madebybye/esp32-mac/renders/fit_gauge.png

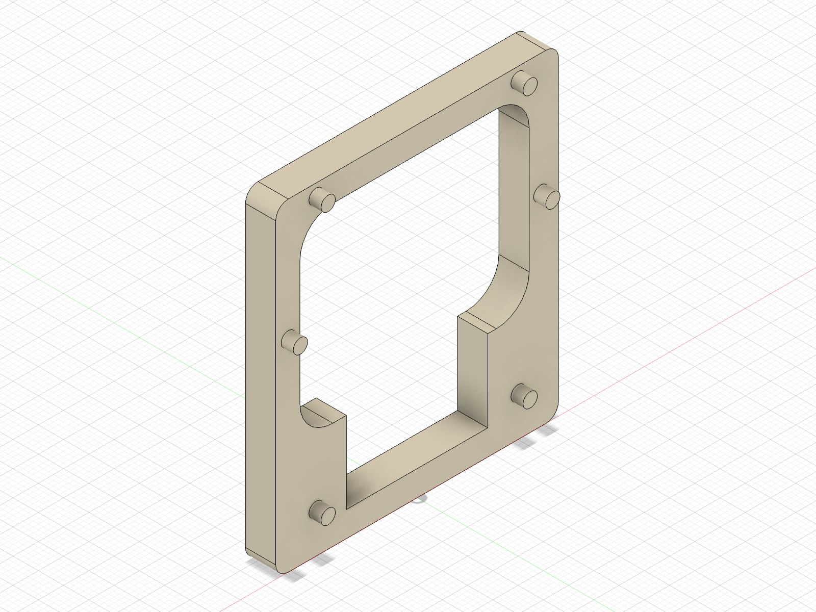
renders/fit_gauge.png
