madebybye/esp32-mac/renders/section.png

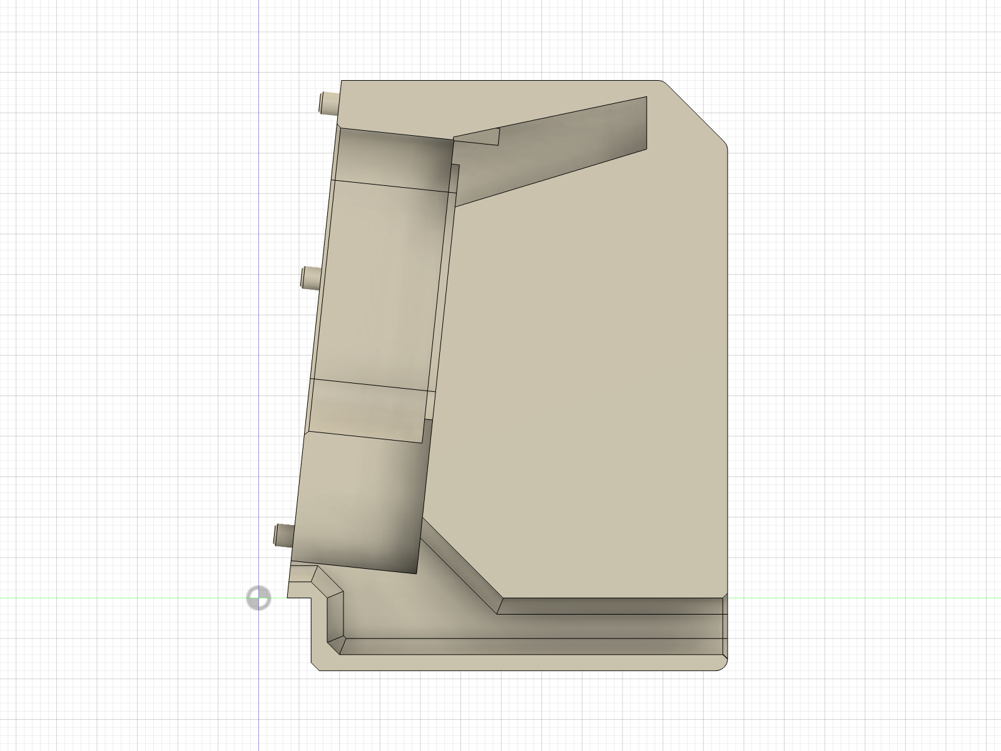
renders/section.png
