madebybye/esp32-mac/renders/parts/Body_front.png

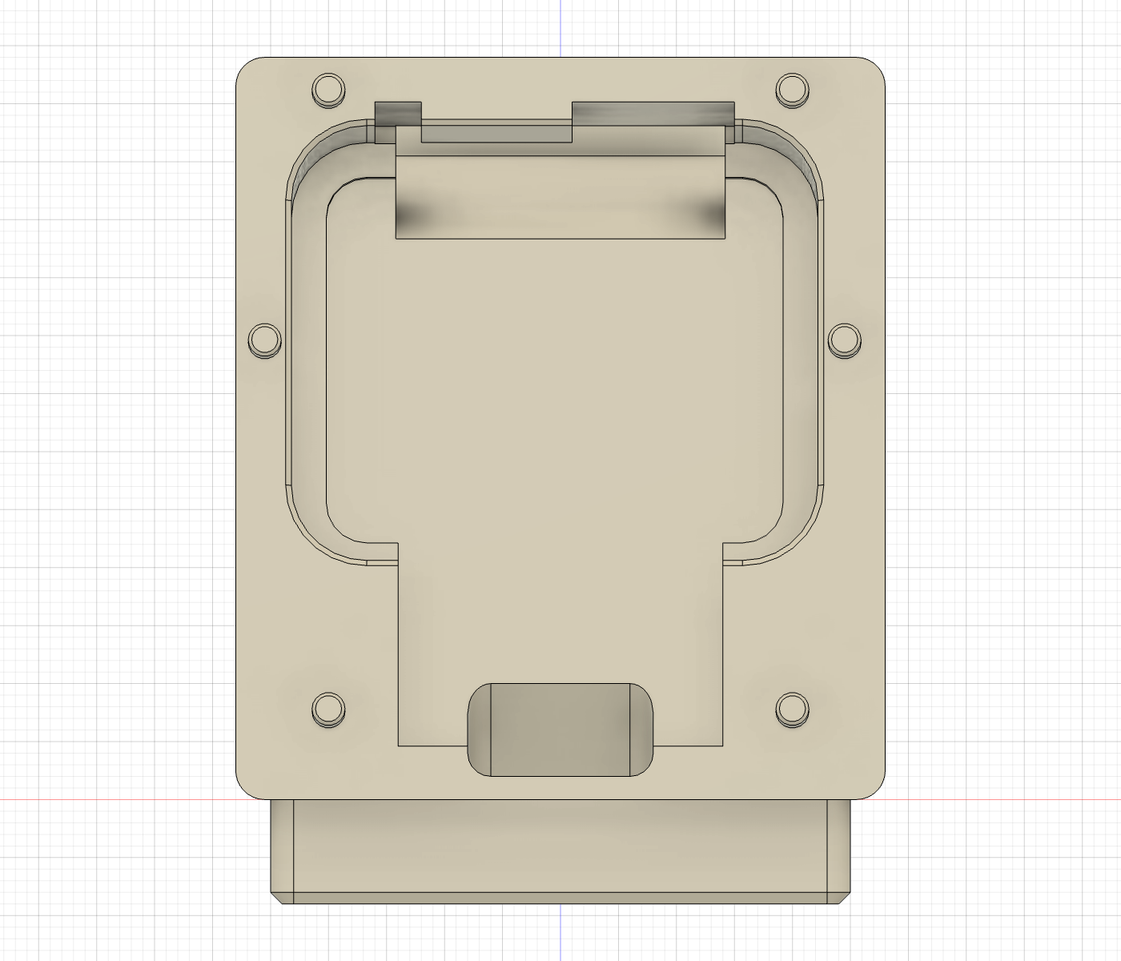
renders/parts/Body_front.png
