madebybye/esp32-mac/renders/parts/Body_iso-top-right.png

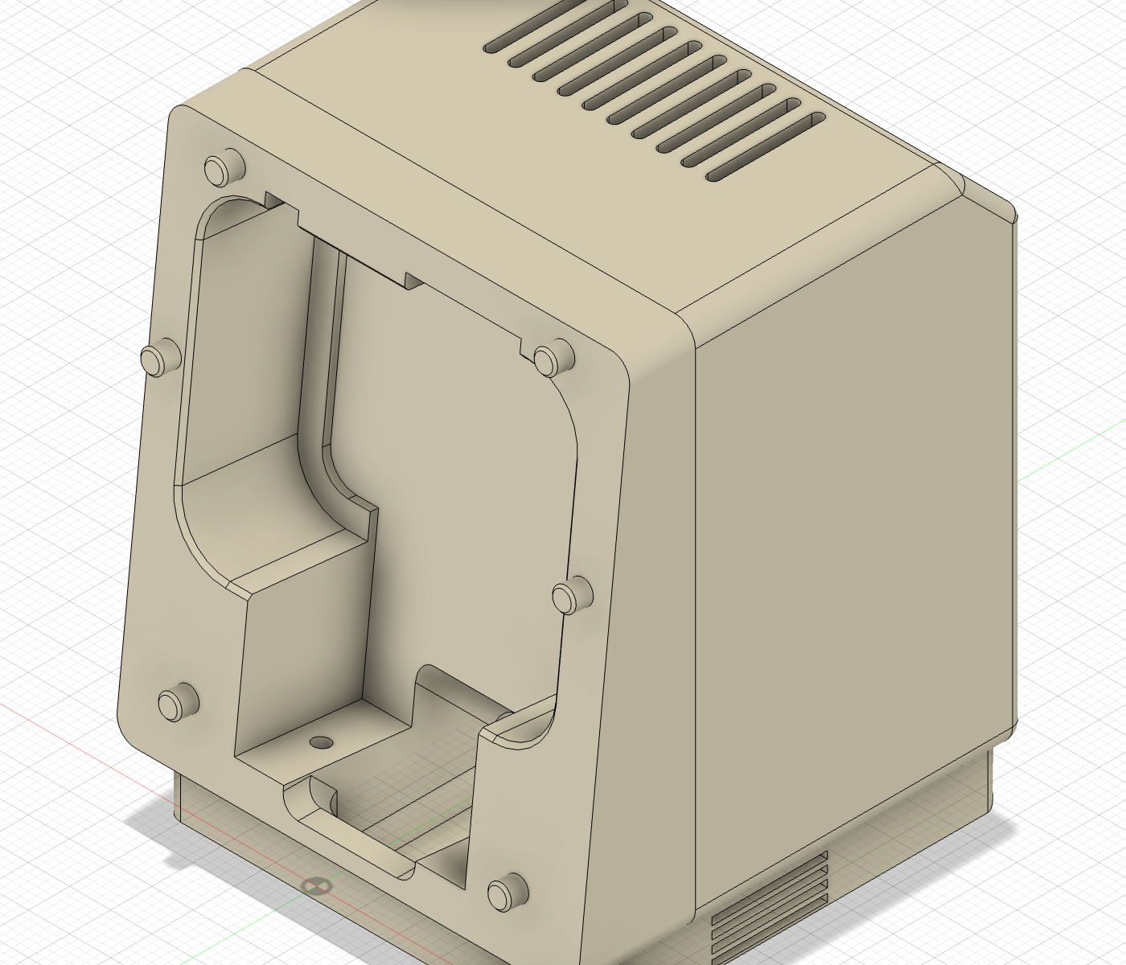
renders/parts/Body_iso-top-right.png
