madebybye/esp32-mac/renders/parts/Body_left.png

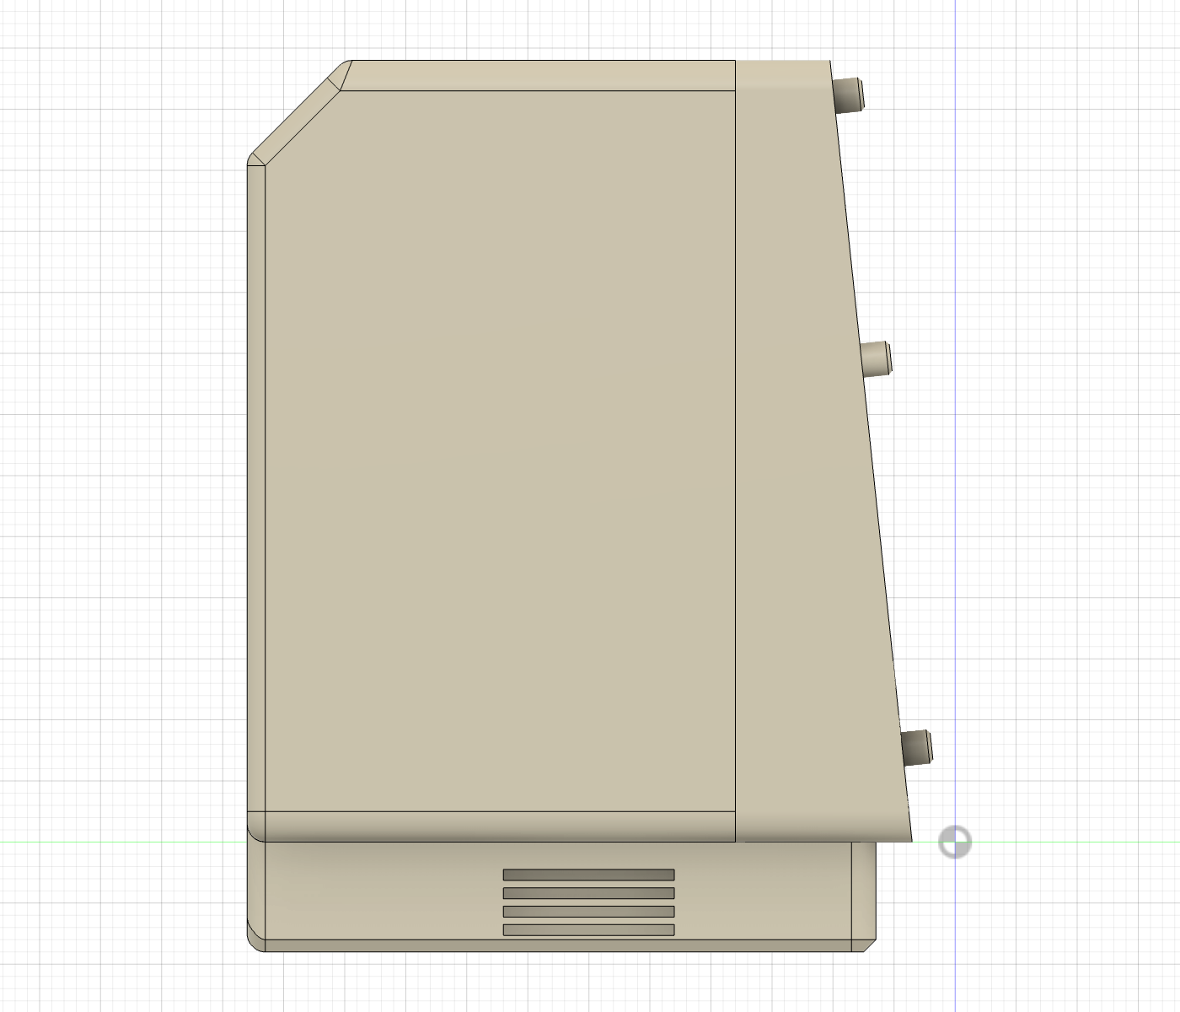
renders/parts/Body_left.png
