madebybye/esp32-mac/renders/parts/FacePlate_front.png

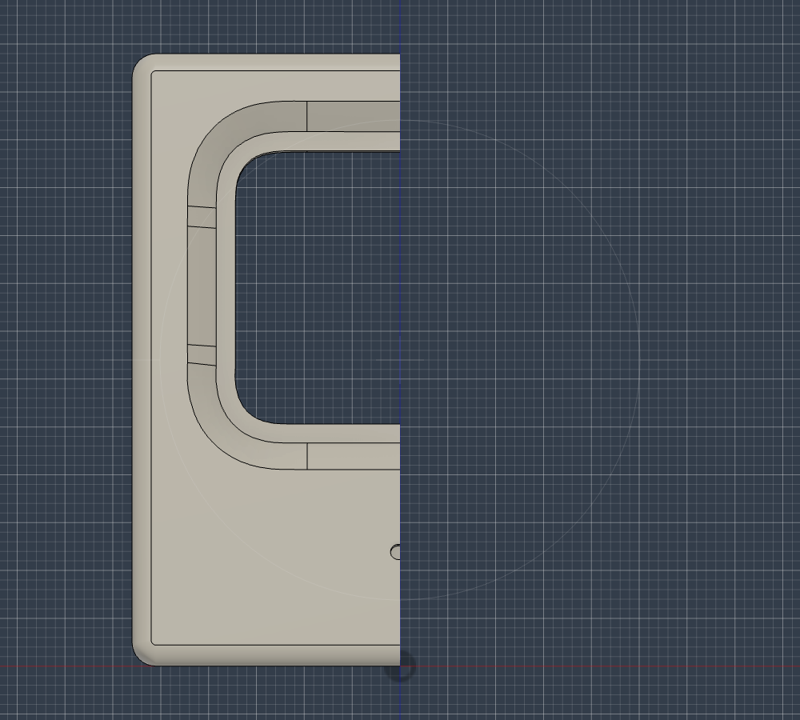
renders/parts/FacePlate_front.png
