madebybye/esp32-mac/renders/parts/FacePlate_iso-top-right.png

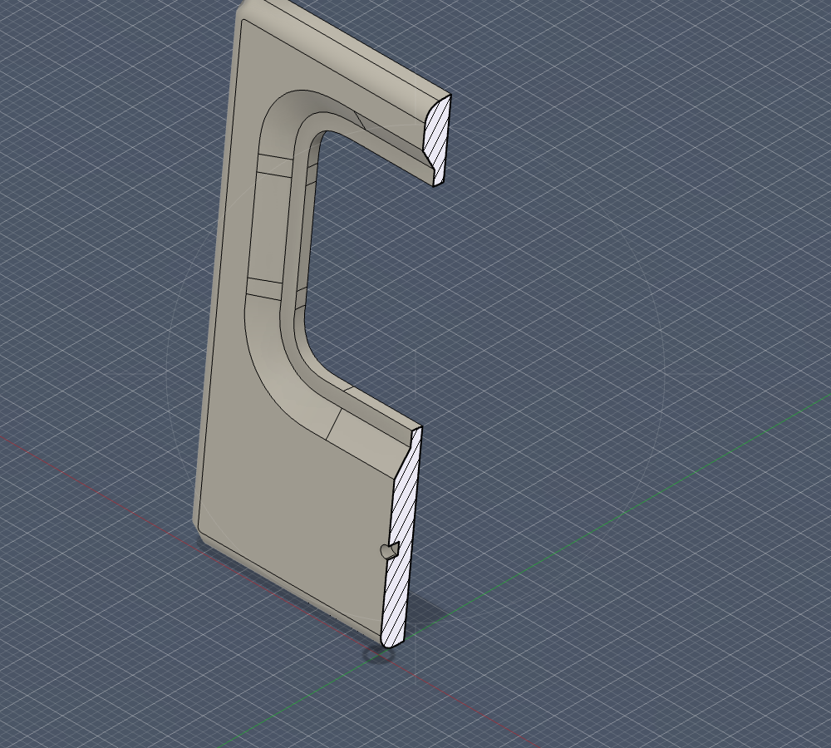
renders/parts/FacePlate_iso-top-right.png
