madebybye/esp32-mac/renders/parts/FacePlate_left.png

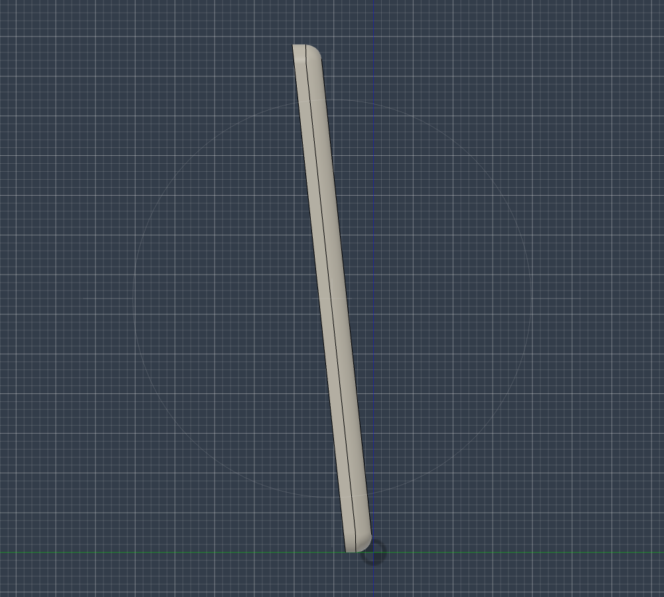
renders/parts/FacePlate_left.png
