madebybye/esp32-mac/renders/parts/FacePlate_sheet.png

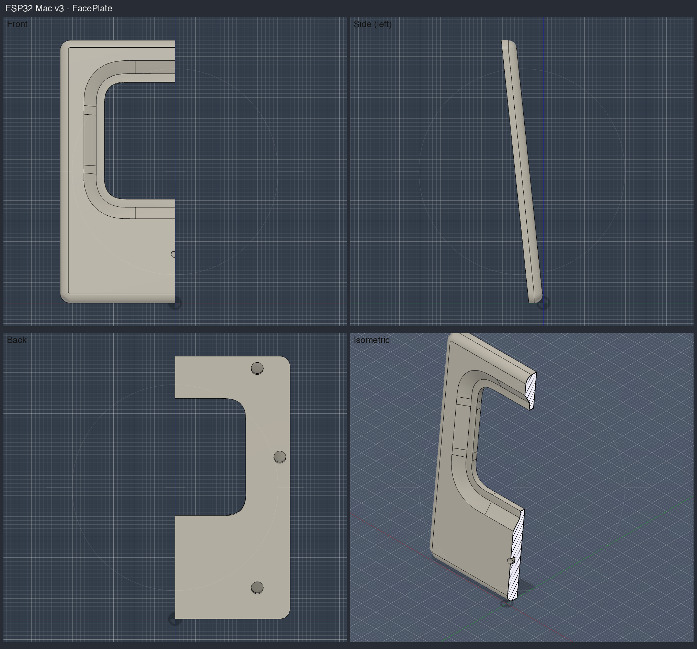
renders/parts/FacePlate_sheet.png
