madebybye/esp32-mac/renders/parts/FitGauge_back.png

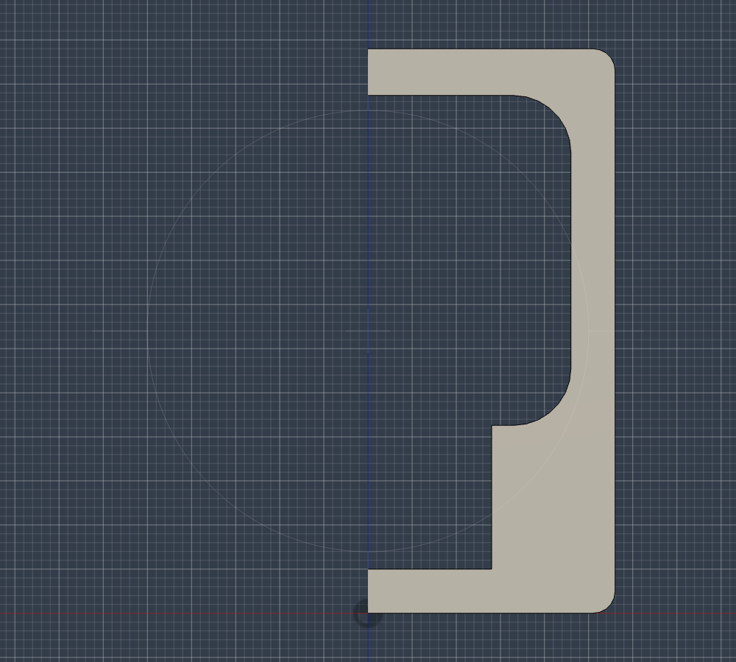
renders/parts/FitGauge_back.png
