madebybye/esp32-mac/renders/parts/FitGauge_sheet.png

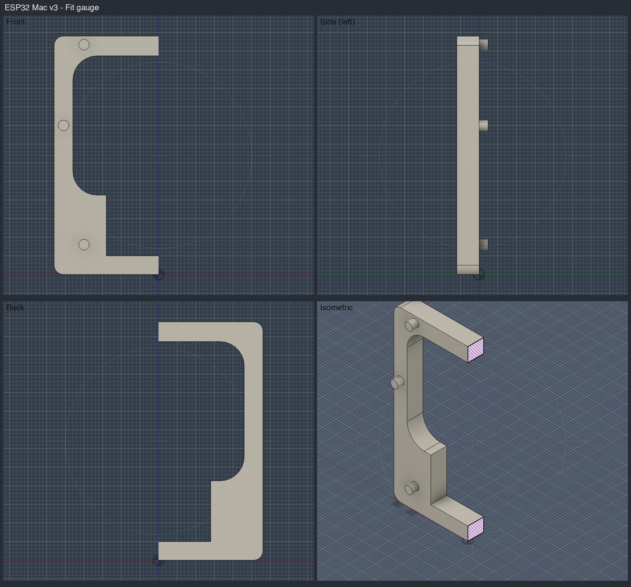
renders/parts/FitGauge_sheet.png
