madebybye/esp32-mac/renders/parts/Assembly_no_device_front.png

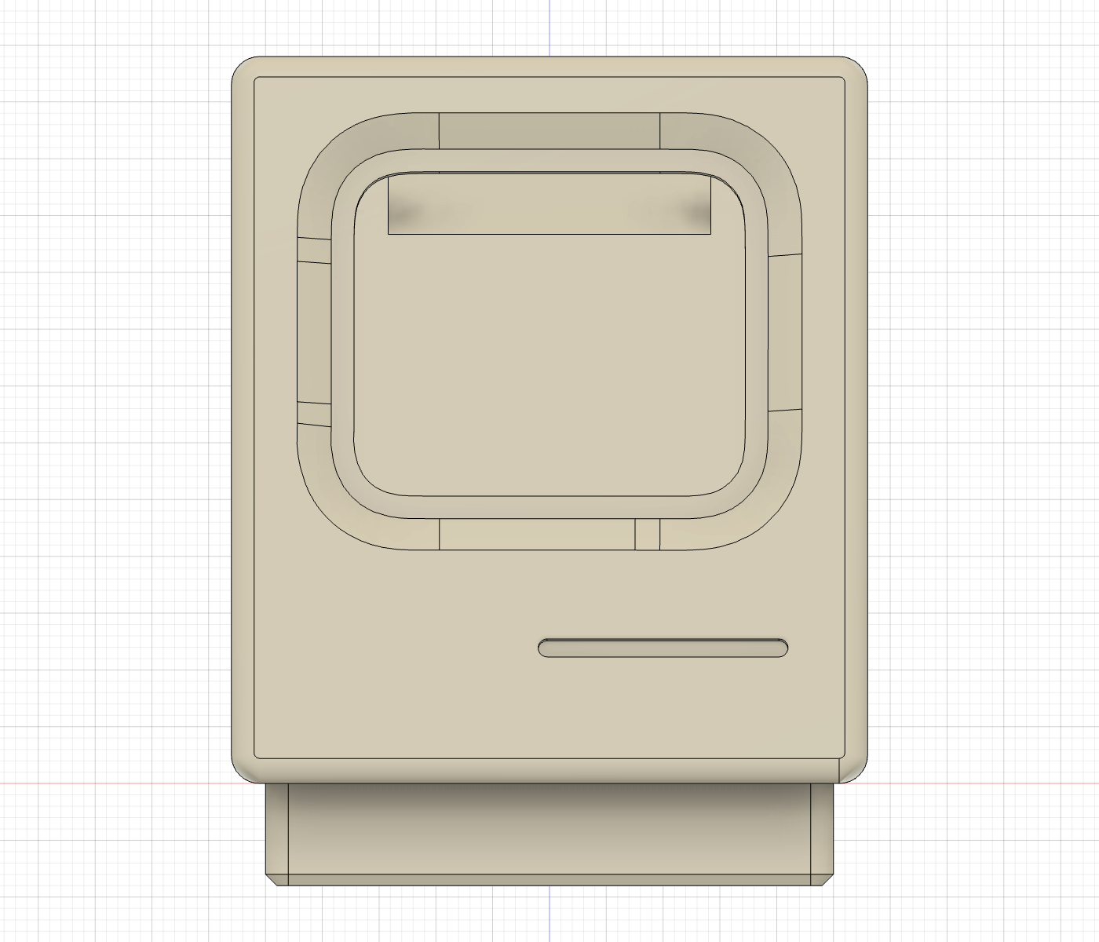
renders/parts/Assembly_no_device_front.png
