madebybye/esp32-mac/renders/parts/Assembly_no_device_iso-top-right.png

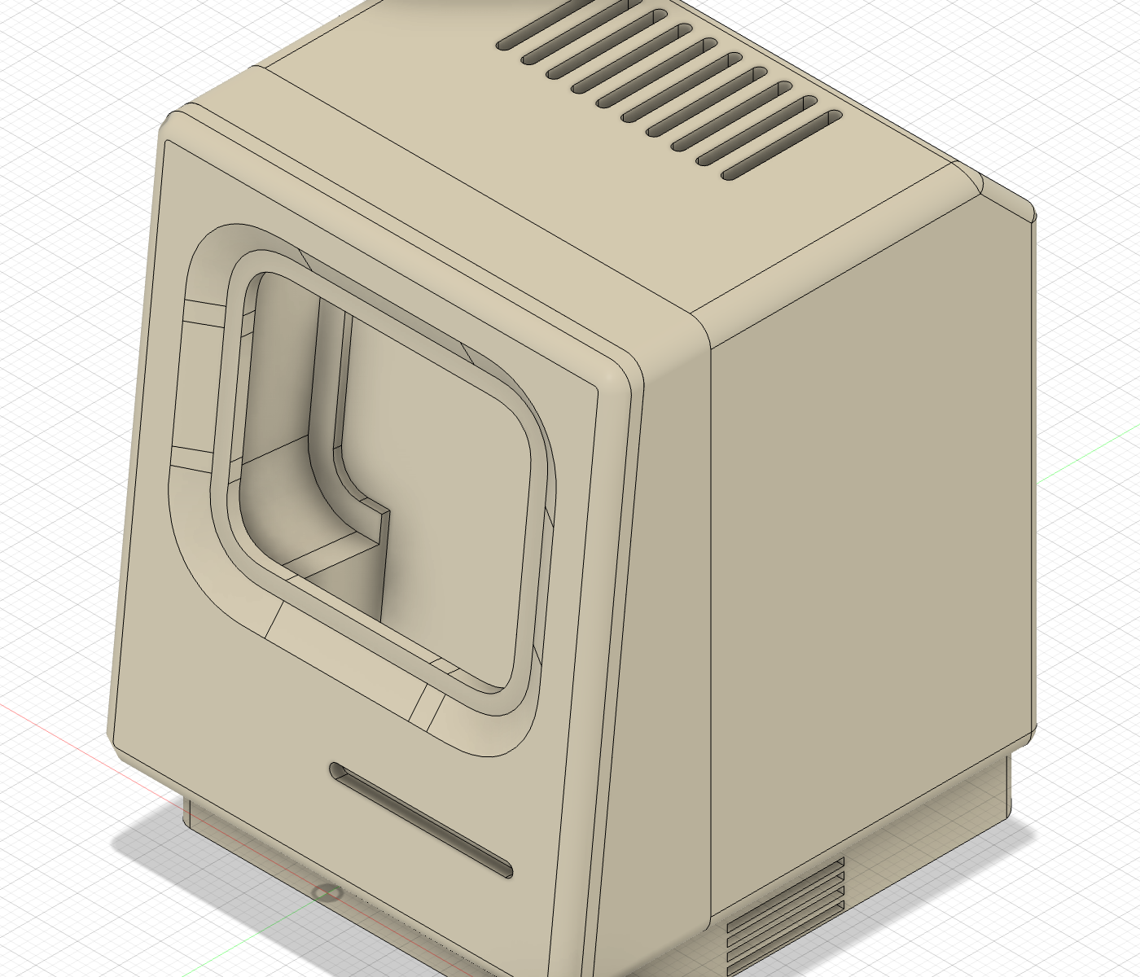
renders/parts/Assembly_no_device_iso-top-right.png
