madebybye/esp32-mac/renders/parts/Assembly_no_device_left.png

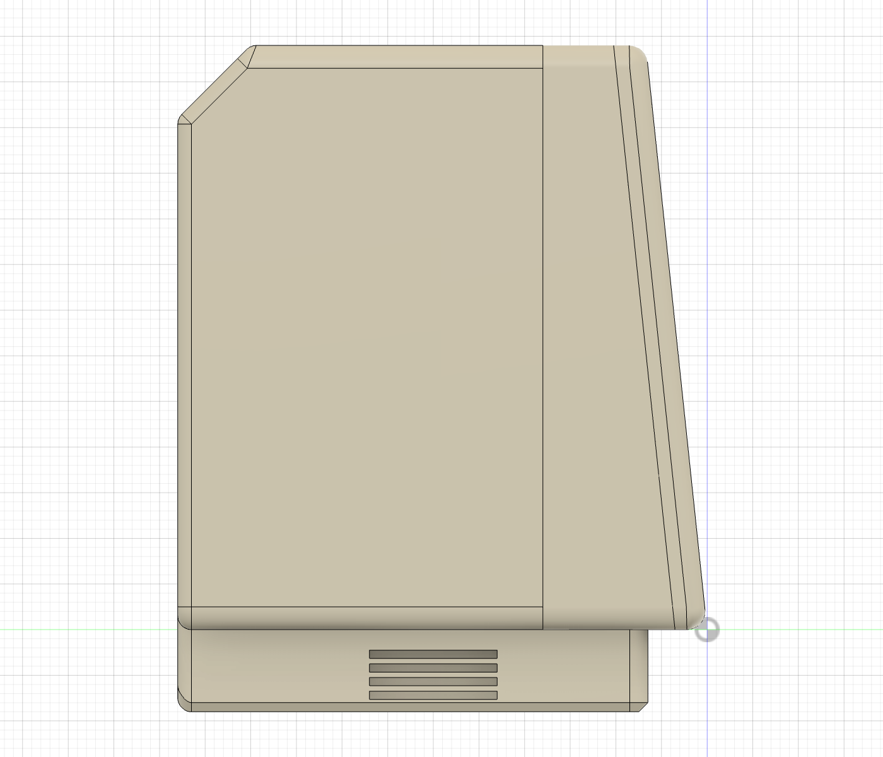
renders/parts/Assembly_no_device_left.png
